notam02/Teensy-Head-Tracker/src/name.c

#include "usb_names.h"

// Edit these lines to create your own name.  The length must
// match the number of characters in your custom name.
#define MIDI_NAME   {'T', 'e', 'e', 'n', 's', 'y', ' ', 'H', 'e', 'a', 'd', ' ', 'T', 'r', 'a', 'c', 'k', 'e', 'r'}
#define MIDI_NAME_LEN  19

// Do not change this part.  This exact format is required by USB.
struct usb_string_descriptor_struct usb_string_product_name = {
        2 + MIDI_NAME_LEN * 2,
        3,
        MIDI_NAME
};
